goopypanther/fnir/firmware/2494_adc.c

/** @file 2494_adc.c
* @brief 2494 ADC Communication Library
* @author Jeremy Ruhland
* @date 8/2014
*/

#include "includes.h"

/** Data fields stored inside ADC chip.
*
*/
typedef union {
    /** Structured bitfield for easy settings */
    struct {
        uint8_t preamble : 2; /**< Preamble bits, identical for all messages */
        uint8_t en       : 1; /**< Enable bit selects adc enable */
        uint8_t sgl      : 1; /**< Bipolar/unipolar mode selection bit */
        uint8_t odd      : 1; /**< Selects between even/odd bit number */
        uint8_t a        : 3; /**< Address of channel selected for conversion */
        uint8_t en2      : 1; /**< Second enable bit selected if settings have changed */
        uint8_t im       : 1; /**< Selects internal/external voltage source */
        uint8_t f        : 2; /**< Selects powerline frequency rejection mode */
        uint8_t spd      : 1; /**< Selects conversion speed & auto calibration */
        uint8_t gs       : 3; /**< Configures internal gain stage */
    } bitfield;
    /** Binary type for SPI transmission */
    uint16_t bin;
} adcMemory_t;

void adcInit(void) {}

adcReturn_t adcSelect(adcState_t adcState,
                      adcChannelType_t adcChannelType,
                      adcRejectionMode_t adcRejectionMode,
                      adcSpeed_t adcSpeed,
                      adcGain_t adcGain) {

    adcMemory_t adcMemory;
    adcReturn_t adcReturn;
    uint8_t adcReturnBuffer[3];

    adcMemory.bitfield.preamble = 0x02; // All commands begin with 0b10

    // Set enable bits
    switch (adcState) {
        case DISABLE :
            adcMemory.bitfield.en = 0x00;
            break;
        case ENABLE :
            adcMemory.bitfield.en = 0x01;
            adcMemory.bitfield.en2 = 0x01;
            break;
        case REPEAT :
            adcMemory.bitfield.en = 0x01;
            adcMemory.bitfield.en2 = 0x00;
            break;
        default:
            break;
    }

    // Set bits to select which bipolar/UNIPOLAR channel to mux into adc
    switch (adcChannelType) {
        case BIPOLAR_CH_0_1 :
            adcMemory.bitfield.sgl = 0x00;
            adcMemory.bitfield.odd = 0x00;
            adcMemory.bitfield.a = 0x00;
            adcMemory.bitfield.im = 0x00;
            break;
        case BIPOLAR_CH_1_0 :
            adcMemory.bitfield.sgl = 0x00;
            adcMemory.bitfield.odd = 0x01;
            adcMemory.bitfield.a = 0x00;
            adcMemory.bitfield.im = 0x00;
            break;
        case BIPOLAR_CH_2_3 :
            adcMemory.bitfield.sgl = 0x00;
            adcMemory.bitfield.odd = 0x00;
            adcMemory.bitfield.a = 0x01;
            adcMemory.bitfield.im = 0x00;
            break;
        case BIPOLAR_CH_3_2 :
            adcMemory.bitfield.sgl = 0x00;
            adcMemory.bitfield.odd = 0x01;
            adcMemory.bitfield.a = 0x01;
            adcMemory.bitfield.im = 0x00;
            break;
        case BIPOLAR_CH_4_5 :
            adcMemory.bitfield.sgl = 0x00;
            adcMemory.bitfield.odd = 0x00;
            adcMemory.bitfield.a = 0x02;
            adcMemory.bitfield.im = 0x00;
            break;
        case BIPOLAR_CH_5_4 :
            adcMemory.bitfield.sgl = 0x00;
            adcMemory.bitfield.odd = 0x01;
            adcMemory.bitfield.a = 0x02;
            adcMemory.bitfield.im = 0x00;
            break;
        case BIPOLAR_CH_6_7 :
            adcMemory.bitfield.sgl = 0x00;
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
            break;
        default :
            break;
    }

    // Put new command into adc, return result
    adcReturnBuffer[0] = spiXfr((uint8_t) (adcMemory.bin>>8));
    adcReturnBuffer[1] = spiXfr((uint8_t) adcMemory.bin);
    adcReturnBuffer[2] = spiXfr(0x00);

    if (adcReturnBuffer[0] & (1<<7)) {
        adcReturn.conversionStatus = ONGOING;
    } else {
        adcReturn.conversionStatus = FINISHED;
    }

    if (adcReturnBuffer[0] & (1<<5)) {
        adcReturn.returnSign = POSITIVE;
    } else {
        adcReturn.returnSign = NEGATIVE;
    }

    adcReturn.returnValue = (((uint16_t) adcReturnBuffer[0])<<11) & (((uint16_t) adcReturnBuffer[1])<<4) & (((uint16_t) adcReturnBuffer[2])>>4);

    return (adcReturn);
}
