goopypanther/fnir/firmware/2494_adc.h

/** @file 2494_adc.h
* @brief 2494 ADC Communication Library
* @author Jeremy Ruhland
* @date 8/2014
*
* The adc will begin its measurement after the program calls \ref adcSelect.
* The proper enumerated type names are defined below. When appropriate, such
* as when shutting down the adc or requesting a repeat measurement, null
* types may be used, which will have no effect on the data sent to the adc.
*
* \ref adcSelect returns a struct which contains a conversion status, polarity
* voltage level, which can be used together to determine error conditions and
* adc state.
*
* The following is an example of capturing a positive unipolar voltage level
* referenced to common (ground) and passing it to \c doSomethingWithVoltage :
*
* @code
* adcReturn_t voltageLevel; // adcSelect returns a struct containing voltage,
*                           // conversion status and polarity information
*
* voltageLevel = adcSelect(ENABLE,         // Enable adc
*                          UNIPOLAR_CH_0,  // Select channel 0, ref to common
*                          REJECT_60HZ,    // Reject 60hz powerline noise
*                          AUTO_CALIBRATE, // Slower but more accurate speed
*                          GAIN_1X);       // Unity gain (no amplification)
*
* doSomethingWithVoltage(voltageLevel.returnValue); // Pass voltage to our
*                                                   // function
*
* @endcode
*
* And this is an example of re-running the last conversion:
*
* @code
* voltageLevel = adcSelect(REPEAT,         // Repeat last conversion
*                          NULL_CH,        // Don't change channel
*                          NULL_REJECTION, // or rejection
*                          NULL_SPEED,     // or speed
*                          NULL_GAIN);     // or gain
*
* doSomethingWithVoltage(voltageLevel.returnValue);
*
* @endcode
*
* Or, if you would like to take an internal temperature measurement:
*
* @code
* adcReturn_t voltageLevel; // adcSelect returns a struct containing voltage,
*                           // conversion status and polarity information
*
* voltageLevel = adcSelect(ENABLE,           // Enable adc
*                          INTERNAL_TEMP_CH, // Select channel 0, ref to common
*                          REJECT_60HZ,      // Reject 60hz powerline noise
*                          NULL_SPEED,       // Temp monitor autoselects speed
*                          NULL_GAIN);       // Temp monitor autoselects gain
*
* doSomethingWithVoltage(voltageLevel.returnValue); // Pass voltage to our
*                                                   // function
* @endcode
*/

/** Structure returned by \ref adcSelect
*
*/
typedef struct {
    /** Status of conversion. */
    enum conversionStatus {
        ONGOING, /**< Conversion is still ongoing. */
        FINISHED /**< Conversion has finished. */
    } conversionStatus;
    /** Polarity of measured voltage. */
    enum returnSign {
        POSITIVE, /**< Posivitive voltage measured. */
        NEGATIVE /**< Negative voltage measured. */
    } returnSign;
    uint16_t returnValue; /**< Voltage measured on channel. */
} adcReturn_t;

/** Set mode of ADC
*
*/
typedef enum {
    DISABLE, /**< ADC off. */
    ENABLE, /**< ADC on. */
    REPEAT /**< Repeat previous measurement. */
} adcState_t;

/** Channel number and type for next measurement.
*
*/
typedef enum {
    BIPOLAR_CH_0_1,
    BIPOLAR_CH_1_0,
    BIPOLAR_CH_2_3,
    BIPOLAR_CH_3_2,
    BIPOLAR_CH_4_5,
    BIPOLAR_CH_5_4,
    BIPOLAR_CH_6_7,
    BIPOLAR_CH_7_6,
    BIPOLAR_CH_8_9,
    BIPOLAR_CH_9_8,
    BIPOLAR_CH_10_11,
    BIPOLAR_CH_11_10,
    BIPOLAR_CH_12_13,
    BIPOLAR_CH_13_12,
    BIPOLAR_CH_14_15,
    BIPOLAR_CH_15_14,
    UNIPOLAR_CH_0,
    UNIPOLAR_CH_1,
    UNIPOLAR_CH_2,
    UNIPOLAR_CH_3,
    UNIPOLAR_CH_4,
    UNIPOLAR_CH_5,
    UNIPOLAR_CH_6,
    UNIPOLAR_CH_7,
    UNIPOLAR_CH_8,
    UNIPOLAR_CH_9,
    UNIPOLAR_CH_10,
    UNIPOLAR_CH_11,
    UNIPOLAR_CH_12,
    UNIPOLAR_CH_13,
    UNIPOLAR_CH_14,
    UNIPOLAR_CH_15,
    INTERNAL_TEMP_CH,
    NULL_CH
} adcChannelType_t;

/** Frequency of powerline noise rejection filter.
*
*/
typedef enum {
    REJECT_50HZ,
    REJECT_60HZ,
    REJECT_50HZ_60HZ,
    NULL_REJECTION
} adcRejectionMode_t;

/** Speed of conversion.
*
*/
typedef enum {
    AUTO_CALIBRATE, /**< Slower, more accurate. Automatically offsets error. */
    DOUBLE_SPEED, /**< Faster but less accurate. */
    NULL_SPEED
} adcSpeed_t;

/** Gain setting of internal amplifier.
*
*/
typedef enum {
    GAIN_1X,
    GAIN_2X,
    GAIN_4X,
    GAIN_8X,
    GAIN_16X,
    GAIN_32X,
    GAIN_64X,
    GAIN_128X,
    NULL_GAIN
} adcGain_t;

/** Initializes adc chip, not currently used.
*
* @return Function does not return a value.
*/
extern void adcInit(void);

/** Starts a new adc conversion and returns last result.
*
* SPI system should be initialized before using this.
*
* @param adcState         Selects current state of adc.
* @param adcChannelType   Selects desired channel from adc.
* @param adcRejectionMode Selects powerline noise rejection filter frequency.
* @param adcSpeed         Selects speed of conversion, normal auto-correcting mode or
*                          double speed (but less accurate).
* @param adcGain          Selects gain stage on adc.
* @return                 Returns struct containing voltage value and adc state
*                          information.
*/
extern adcReturn_t adcSelect(adcState_t adcState,
                             adcChannelType_t adcChannelType,
                             adcRejectionMode_t adcRejectionMode,
                             adcSpeed_t adcSpeed,
                             adcGain_t adcGain);
